ductsoup/Raspberry-Pi-IoT-Water-Quality-Controller/enclosure/IMG_4007.JPG

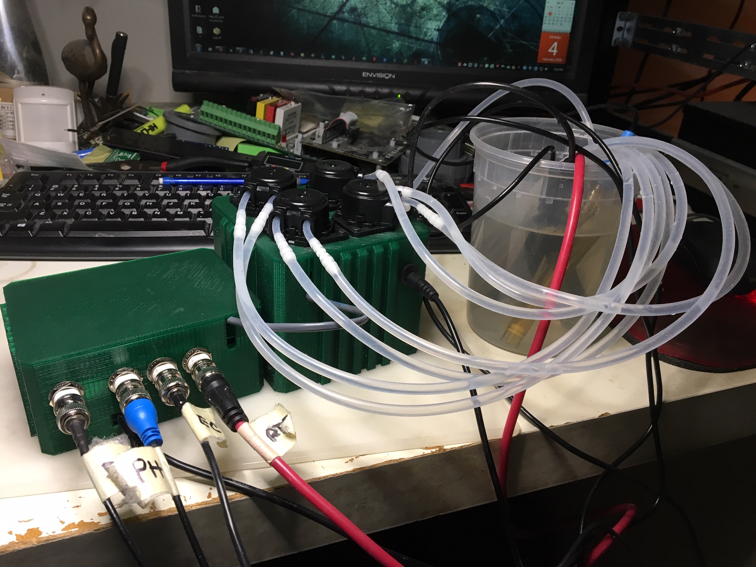
enclosure/IMG_4007.JPG
