ductsoup/Raspberry-Pi-IoT-Water-Quality-Controller/enclosure/IMG_4008.JPG

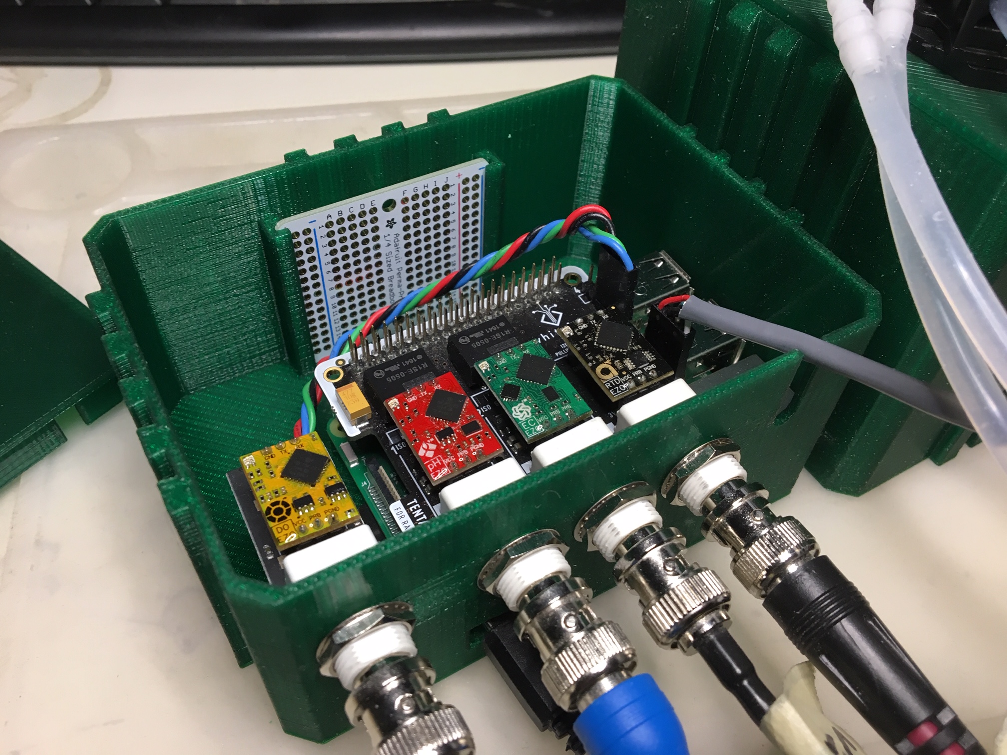
enclosure/IMG_4008.JPG
