ductsoup/Raspberry-Pi-IoT-Water-Quality-Controller/enclosure/IMG_4009.JPG

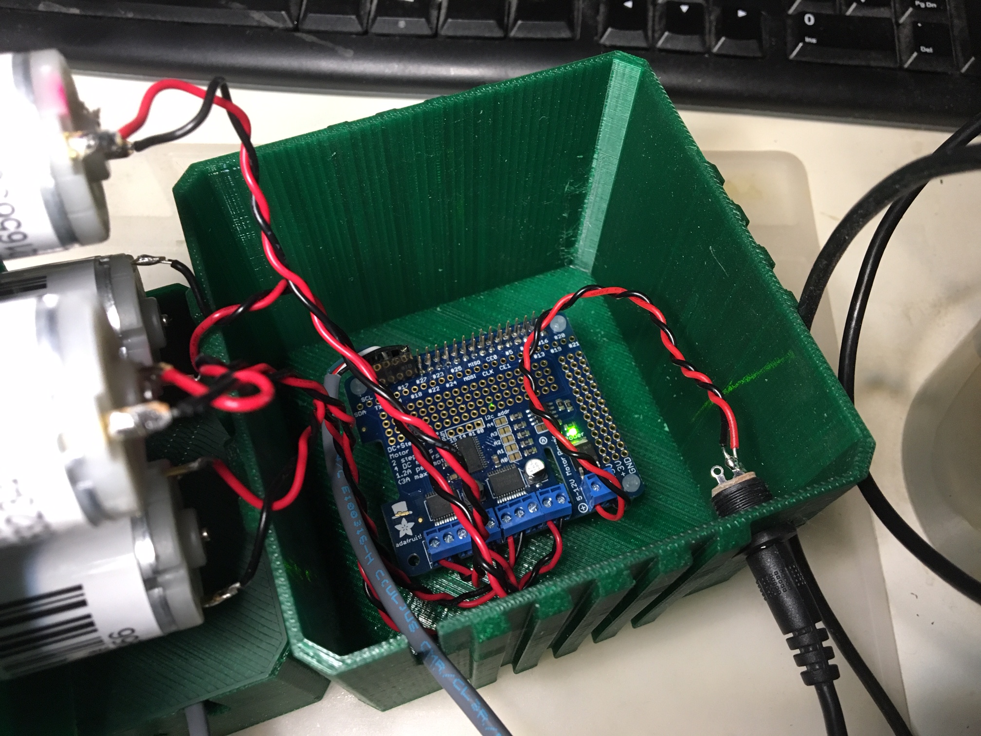
enclosure/IMG_4009.JPG
